AlexGyver/GyverMatrixBT/schemes/mega.jpg

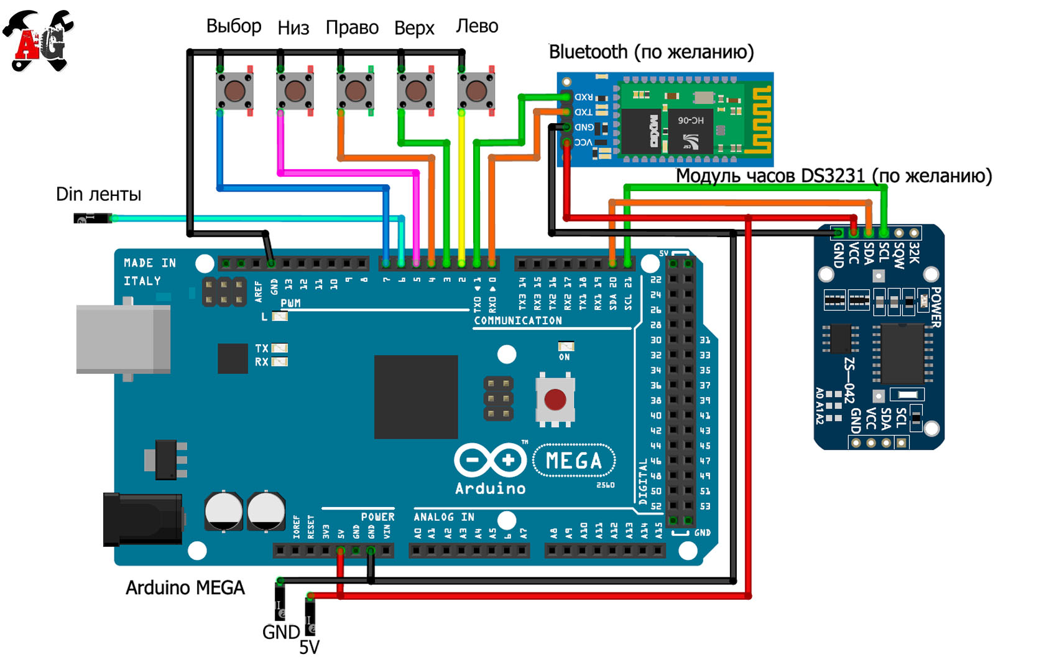
schemes/mega.jpg
