AlexGyver/GyverMatrixBT/schemes/nano.jpg

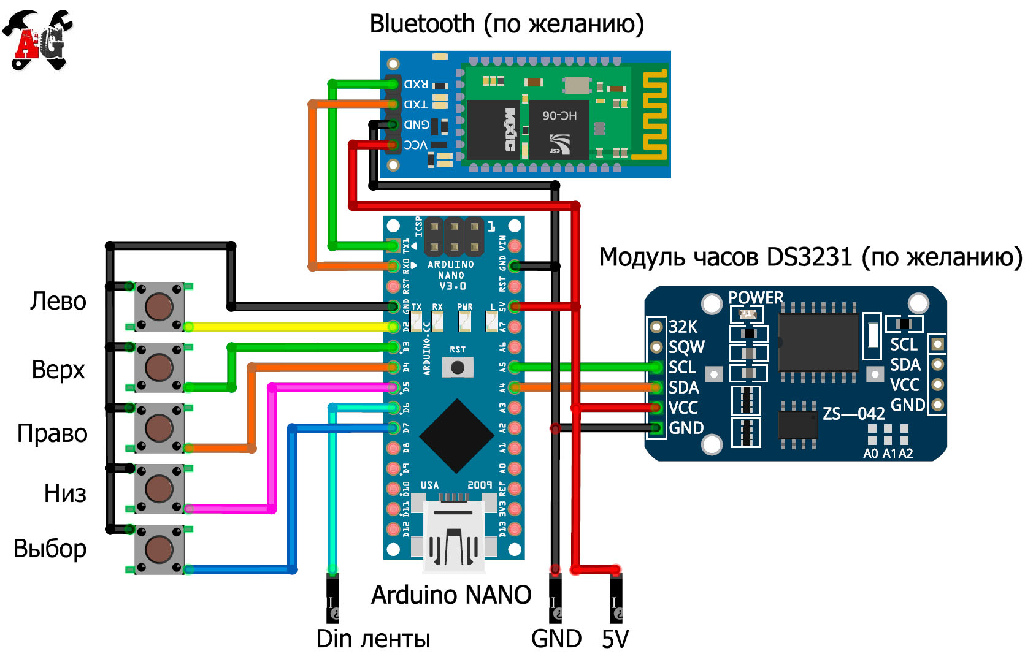
schemes/nano.jpg
