AlexGyver/GyverMatrixBT/schemes/nodemcu.jpg

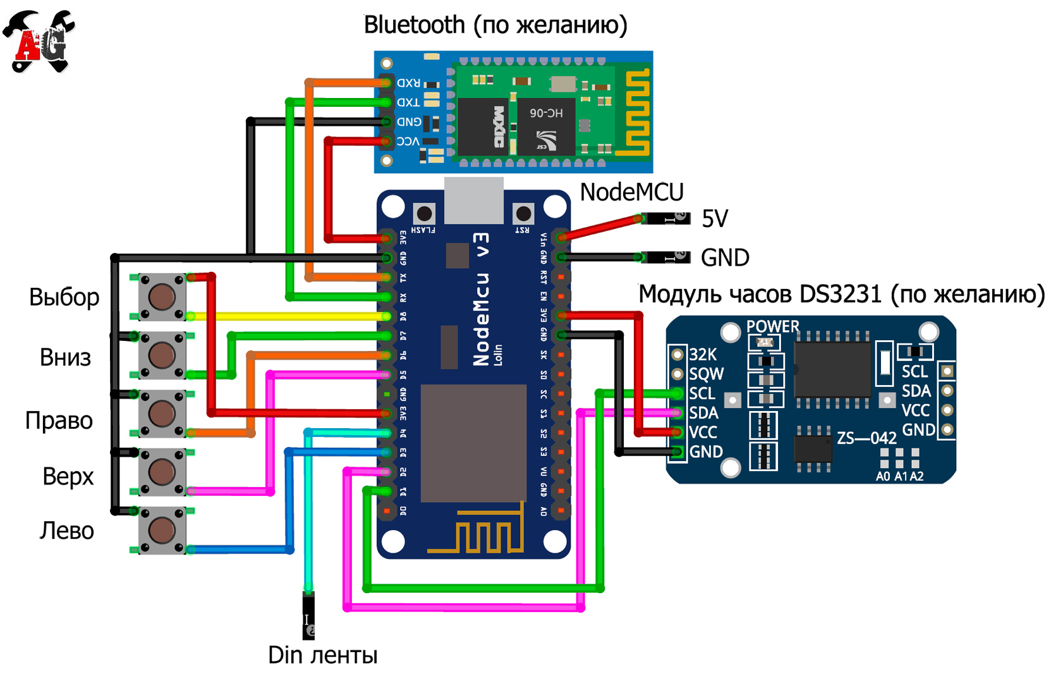
schemes/nodemcu.jpg
