AlexGyver/GyverMatrixBT/schemes/stm32.jpg

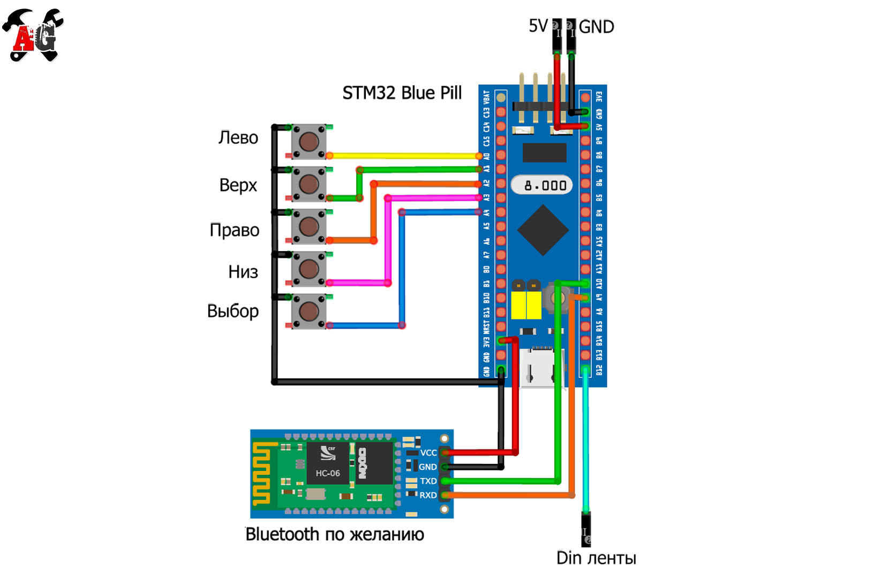
schemes/stm32.jpg
