AlexGyver/GyverMatrixBT/schemes/wemos.jpg

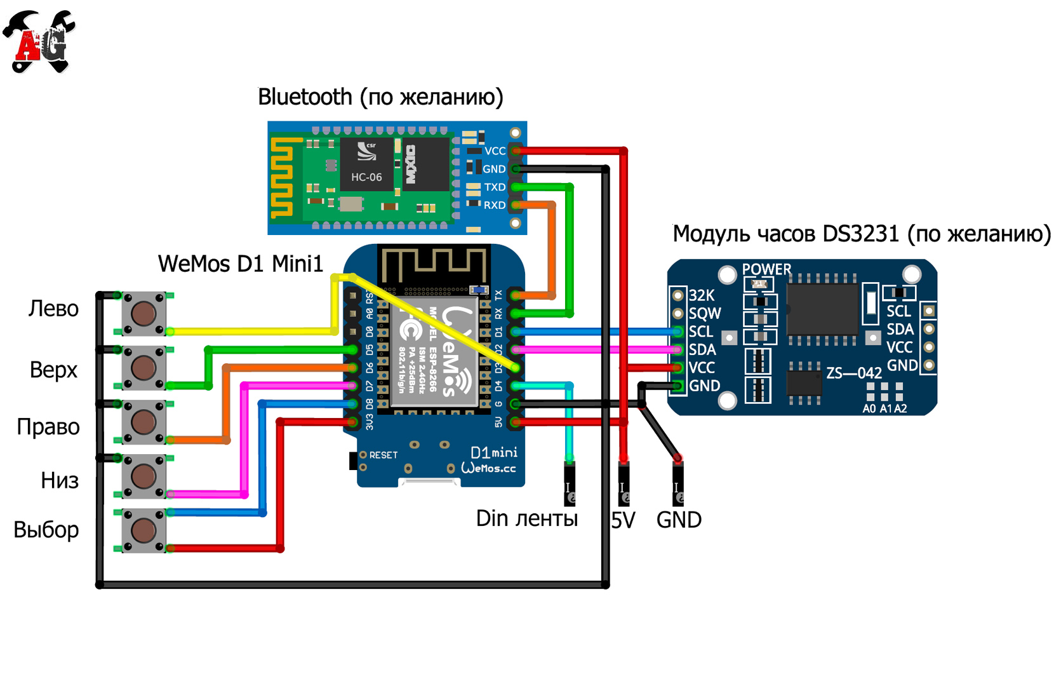
schemes/wemos.jpg
