AlexGyver/GyverMatrixBT/firmware/GyverMatrixOS_v1.12/bitmap2.h

const uint16_t frame00[][16] PROGMEM = {
  {0x0000, 0x0000, 0x0000, 0x0000, 0x3000, 0xF000, 0xF800, 0xF800, 0xF800, 0xF000, 0x3000, 0x3000, 0x3000, 0x0000, 0x0000, 0x0000 },
  {0x0000, 0x0000, 0x0000, 0x40A0, 0xE003, 0xF001, 0xF000, 0xF960, 0xF960, 0xF001, 0xF960, 0xF000, 0xF000, 0x5960, 0x0000, 0x0000 },
  {0x0000, 0x0000, 0x0000, 0x0000, 0x61A0, 0x5960, 0x7200, 0xFE60, 0xF660, 0x3980, 0xE603, 0x6280, 0x5A60, 0x0000, 0x0000, 0x0000 },
  {0x0000, 0x0000, 0x0000, 0x5960, 0xE603, 0x61A0, 0xE603, 0xFEA0, 0xFE80, 0x39A0, 0xE603, 0xFEA0, 0xFE80, 0x7B40, 0x0000, 0x0000 },
  {0x0000, 0x0000, 0x0000, 0x5960, 0xE603, 0x7200, 0x7220, 0xFE80, 0xFEA0, 0xE603, 0x5A60, 0xE603, 0xF660, 0xFE80, 0x39A0, 0x0000 },
  {0x0000, 0x0000, 0x0000, 0x3000, 0x7200, 0xE603, 0xF660, 0xFEA0, 0xFE80, 0x5A60, 0x3160, 0x39A0, 0x39A0, 0x5A60, 0x0000, 0x0000 },
  {0x0000, 0x0000, 0x0000, 0x0000, 0x0000, 0xF660, 0xFE40, 0xF660, 0xFE40, 0xF660, 0xF660, 0xE603, 0x39A0, 0x0000, 0x0000, 0x0000 },
  {0x0000, 0x0000, 0x0000, 0x40A0, 0xF000, 0xF8E0, 0xF000, 0x119D, 0xF000, 0xF000, 0x3160, 0x3160, 0x0000, 0x0000, 0x0000, 0x0000 },
  {0x0000, 0x0000, 0x6120, 0xF800, 0xF800, 0xF800, 0xF000, 0x08FE, 0x119D, 0xF000, 0xE003, 0x0000, 0x0000, 0x0000, 0x0000, 0x0000 },
  {0x0000, 0x0000, 0x6120, 0xF800, 0xF800, 0xF001, 0x28DA, 0x093E, 0xD6C5, 0x18DC, 0x18DC, 0x0000, 0x0000, 0x0000, 0x0000, 0x0000 },
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
  {0x0000, 0x0000, 0x48C0, 0x48C0, 0x48C0, 0x0000, 0x0000, 0x0000, 0x0000, 0x0000, 0x0000, 0x0000, 0x0000, 0x0000, 0x0000, 0x0000 },
};

const uint16_t framesArray[4] = {frame00, frame01, frame02, frame03};
